Atlas-5/Dynamic-suspension-system/Pictures/00af8873-7f91-435a-ae91-4d459b5c4344.jpg

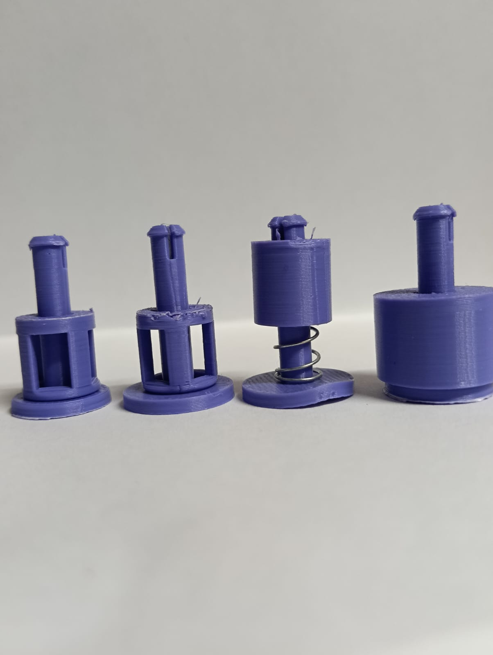
Pictures/00af8873-7f91-435a-ae91-4d459b5c4344.jpg
