Atlas-5/Dynamic-suspension-system/Pictures/39a9ddb1-08d6-4faa-a395-d9c41d649f49.jpg

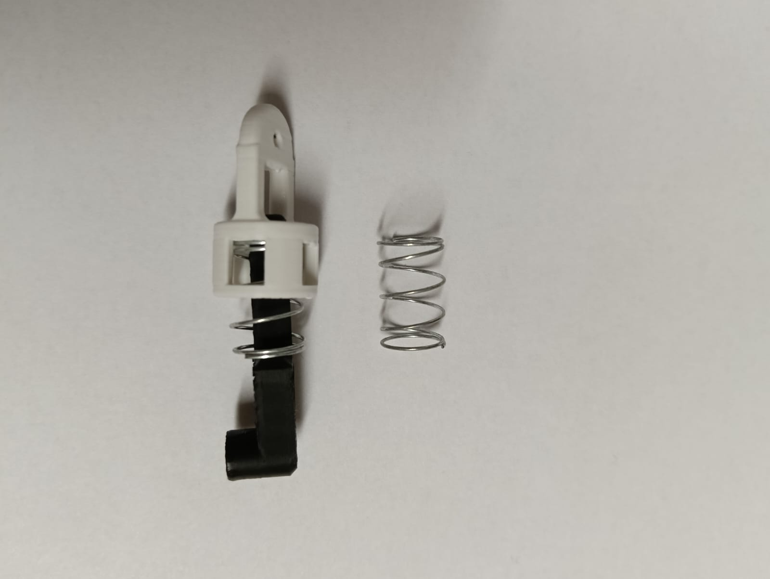
Pictures/39a9ddb1-08d6-4faa-a395-d9c41d649f49.jpg
