Atlas-5/Dynamic-suspension-system/Pictures/99a8557c-0f68-4df7-83fa-4903a3605967.jpg

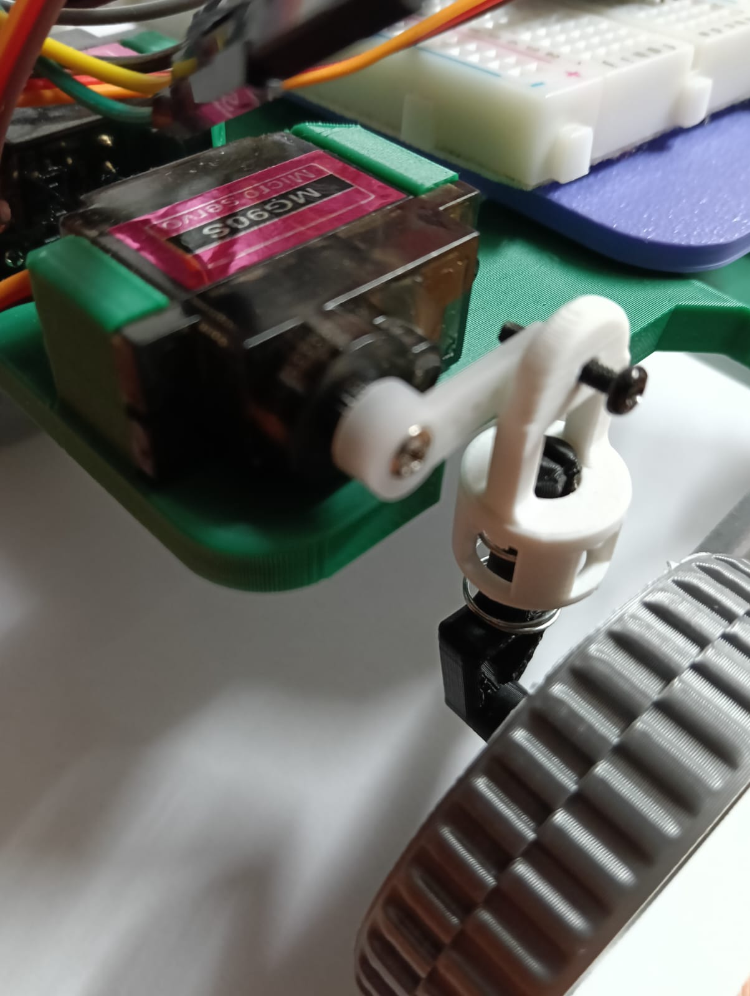
Pictures/99a8557c-0f68-4df7-83fa-4903a3605967.jpg
