Atlas-5/Dynamic-suspension-system/Pictures/aff3a38f-3849-4a3e-81c7-1bab70225882.jpg

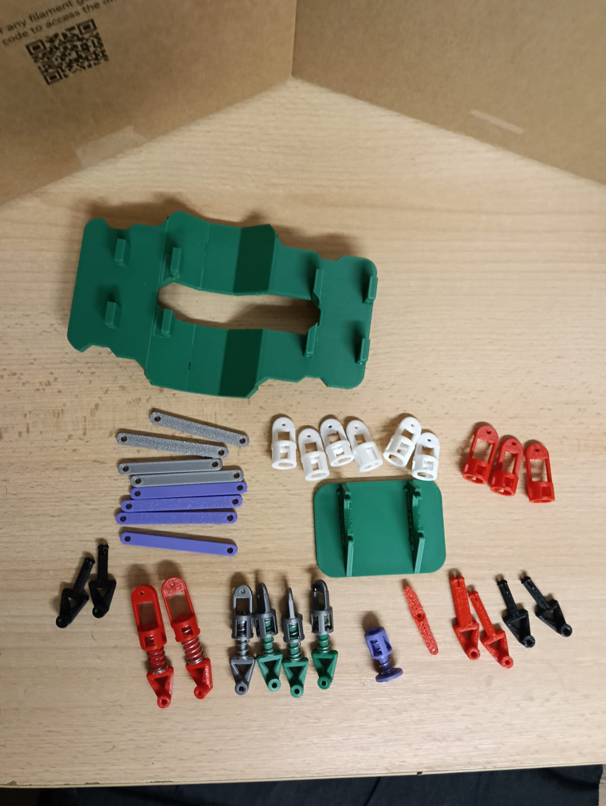
Pictures/aff3a38f-3849-4a3e-81c7-1bab70225882.jpg
