Atlas-5/Dynamic-suspension-system/Pictures/d5f3807e-2c15-4c03-9149-d466c39dcc42.jpg

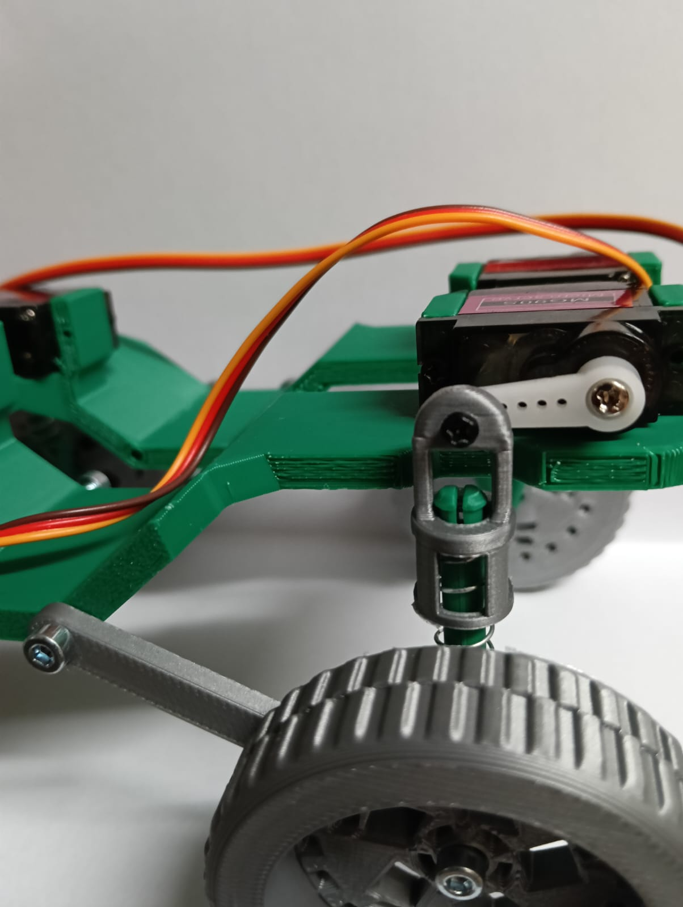
Pictures/d5f3807e-2c15-4c03-9149-d466c39dcc42.jpg
