Atlas-5/Dynamic-suspension-system/Pictures/d86d8c18-dc90-4d3b-8a87-73da1349b741.jpg

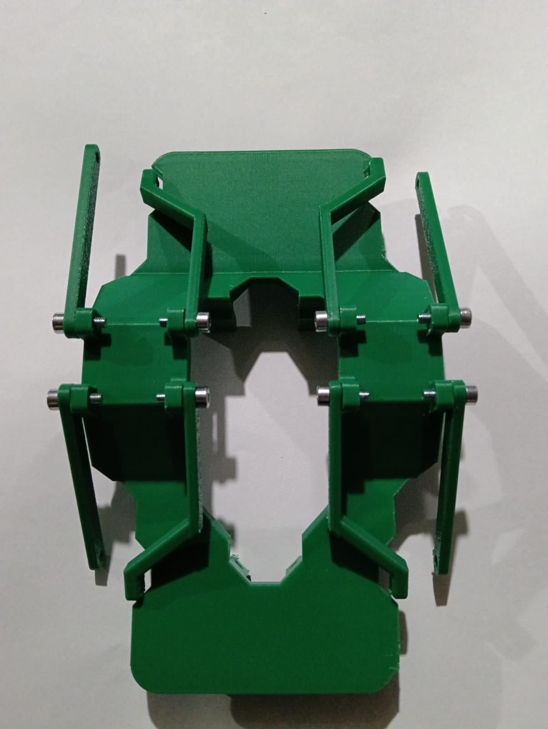
Pictures/d86d8c18-dc90-4d3b-8a87-73da1349b741.jpg
