Atlas-5/Dynamic-suspension-system/3D_Objects/Suport_suspensie_fataV2.stl

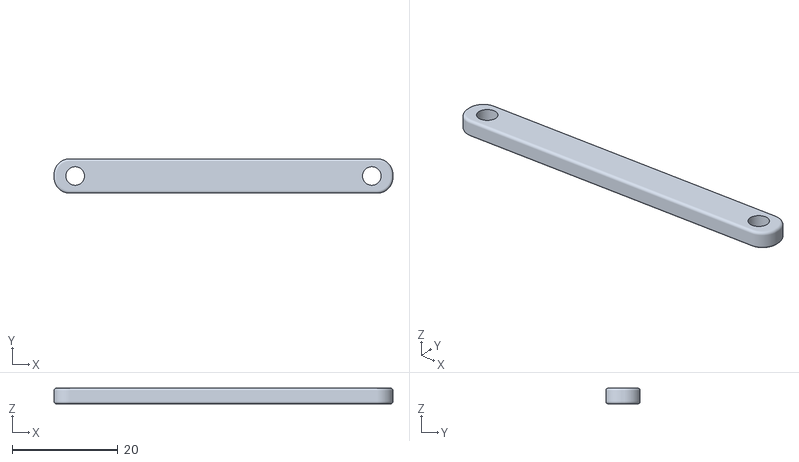
[picture p48: CAD file, 2025-02-22, an earlier design]
3D_Objects/Suport_suspensie_fataV2.stl
64.0 x 6.50 x 3.00
